mdaffarh005-arch/smart-billiard-lighting/3D Design/BOTTOM View.png

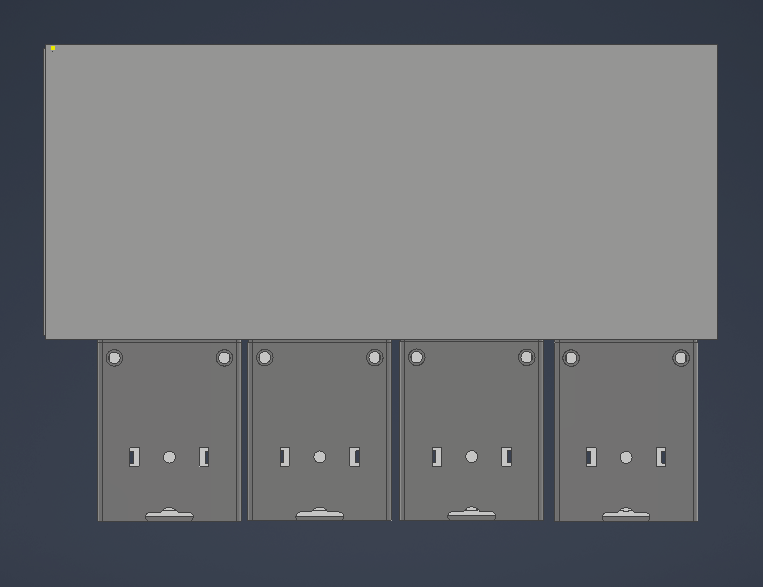
3D Design/BOTTOM View.png
