mdaffarh005-arch/smart-billiard-lighting/3D Design/FRONT View.png

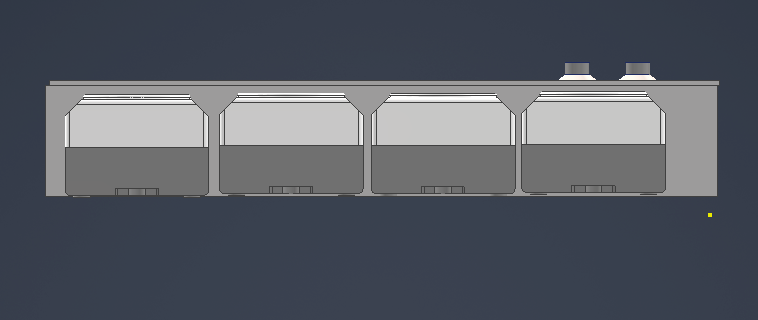
3D Design/FRONT View.png
