mdaffarh005-arch/smart-billiard-lighting/3D Design/LEFT View.png

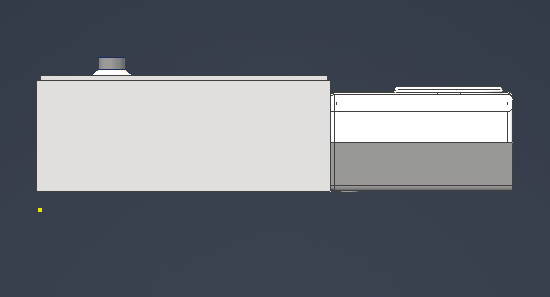
3D Design/LEFT View.png
