mdaffarh005-arch/smart-billiard-lighting/3D Design/RIGHT View.png

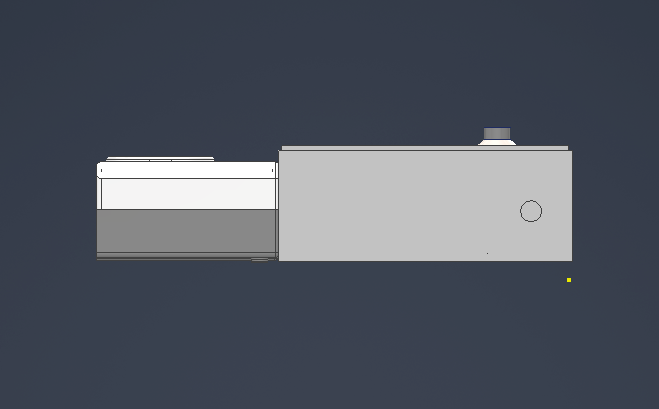
3D Design/RIGHT View.png
