mdaffarh005-arch/smart-billiard-lighting/3D Design/TOP Without Box Cover View.png

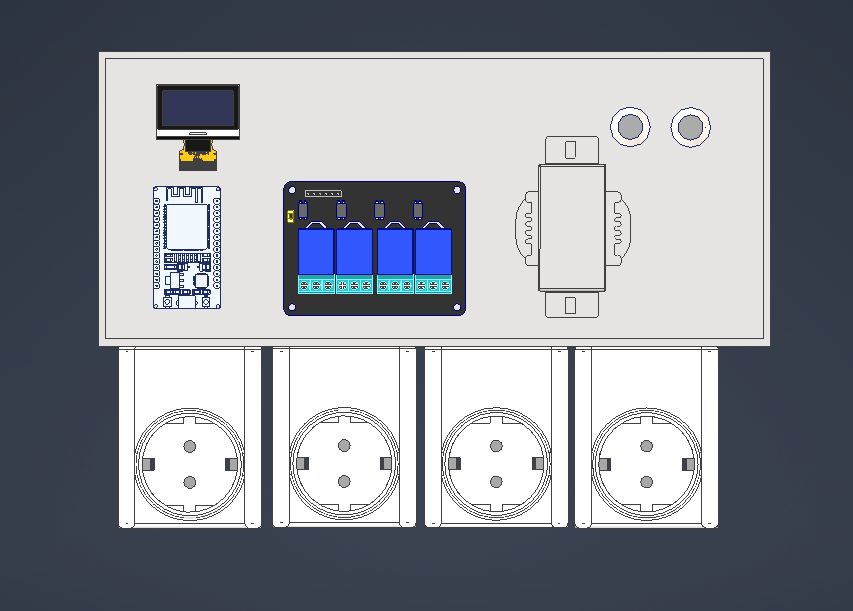
3D Design/TOP Without Box Cover View.png
