mdaffarh005-arch/smart-billiard-lighting/Blok Diagram/Diagram Blok.png

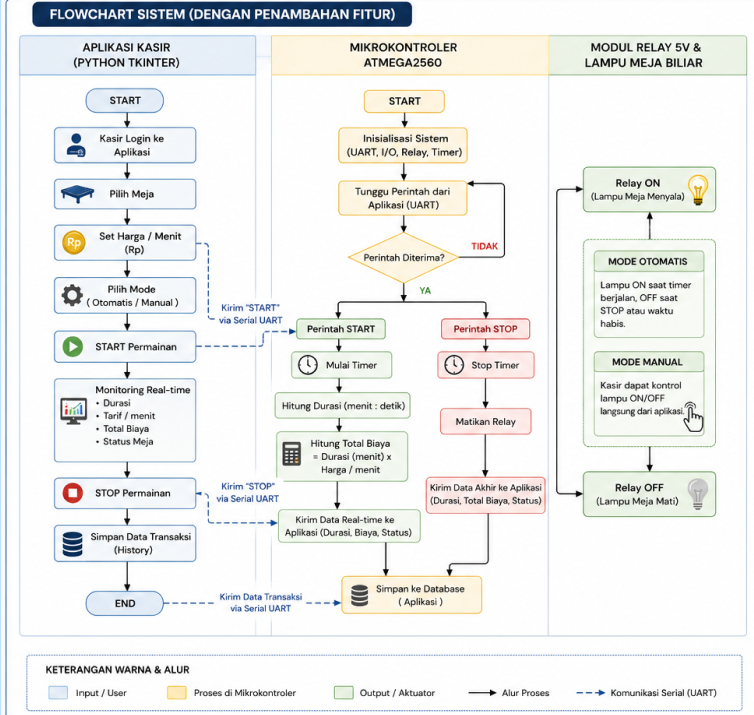
Blok Diagram/Diagram Blok.png
