mdaffarh005-arch/smart-billiard-lighting/Design UI UX/Mockup/desktop-billing V2.png

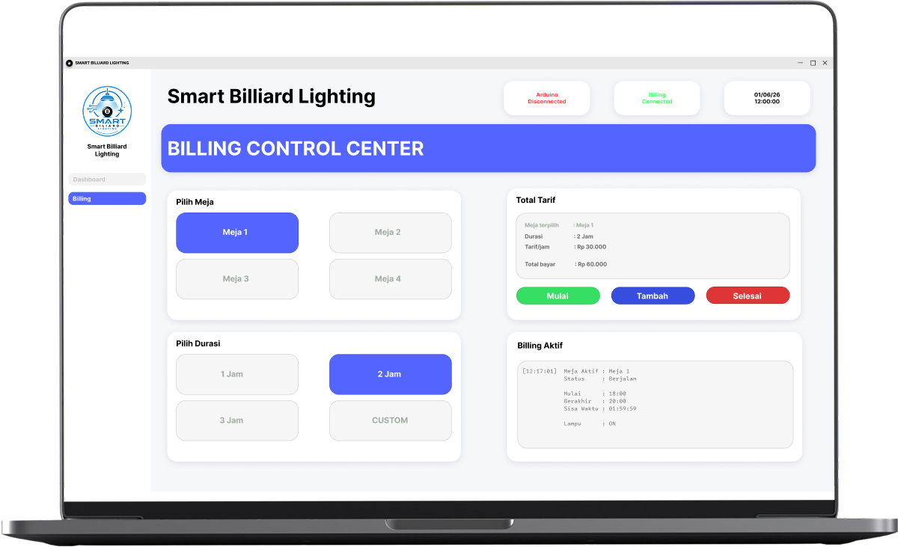
Design UI UX/Mockup/desktop-billing V2.png
