mdaffarh005-arch/smart-billiard-lighting/Design UI UX/Mockup/desktop-dashboard V2.png

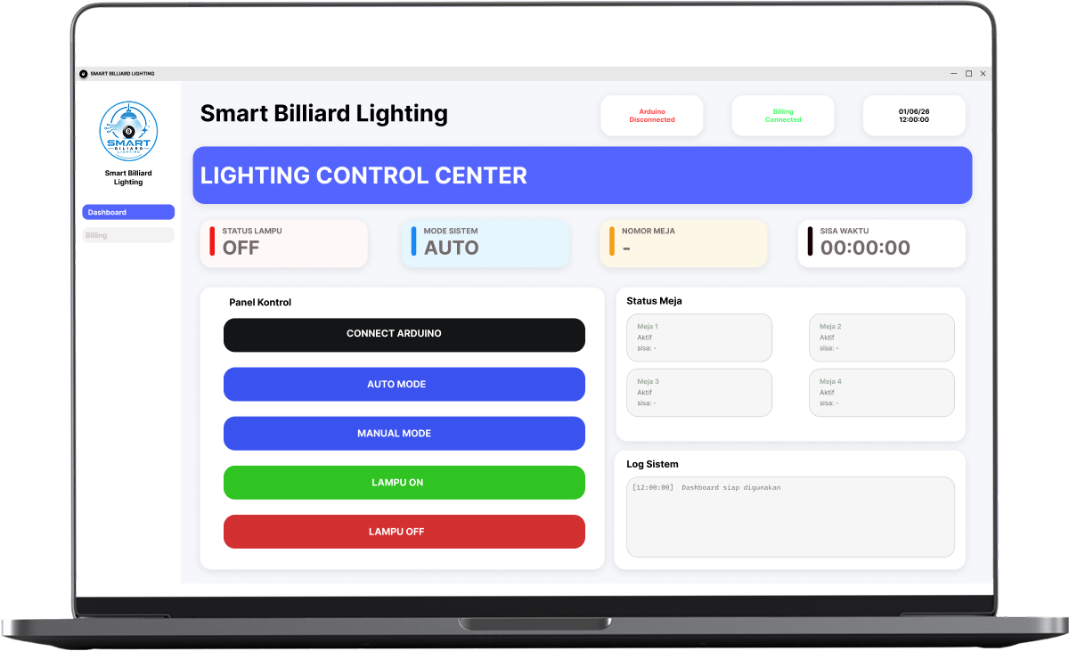
Design UI UX/Mockup/desktop-dashboard V2.png
