mdaffarh005-arch/smart-billiard-lighting/Design UI UX/Screenshot/BILLING.png

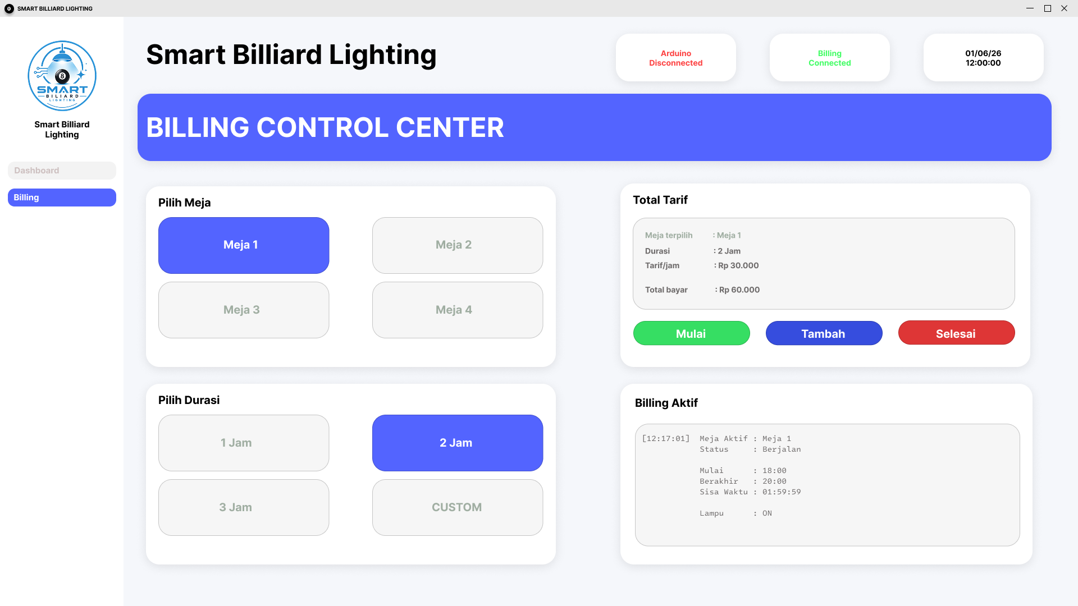
Design UI UX/Screenshot/BILLING.png
