mdaffarh005-arch/smart-billiard-lighting/Design UI UX/Screenshot/screenshot-billing.png

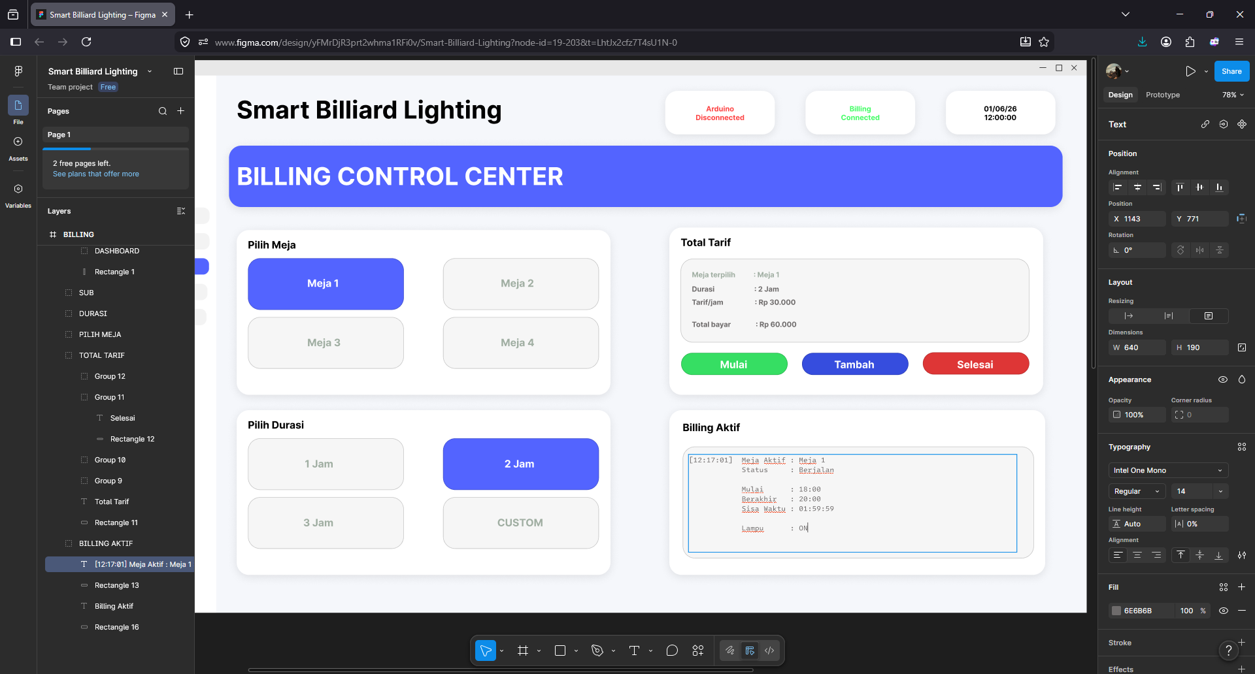
Design UI UX/Screenshot/screenshot-billing.png
