mdaffarh005-arch/smart-billiard-lighting/Design UI UX/Screenshot/screenshot-workspace.png

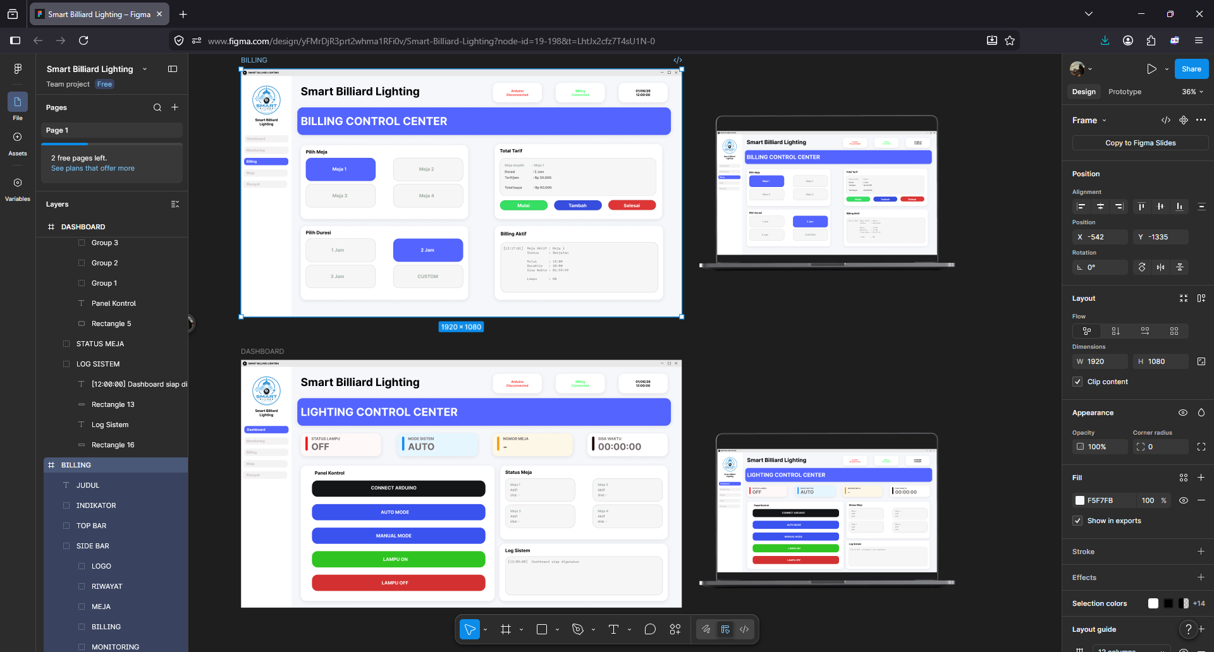
Design UI UX/Screenshot/screenshot-workspace.png
