mdaffarh005-arch/smart-billiard-lighting/Hardware/3D view bottom-smart-biliard-lighting.png

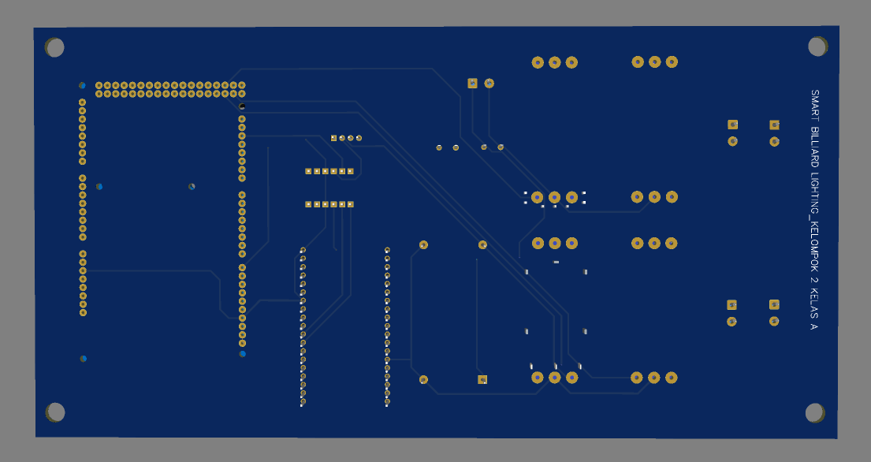
Hardware/3D view bottom-smart-biliard-lighting.png
