mdaffarh005-arch/smart-billiard-lighting/Hardware/3D view top-smart-biliard-lighting.png

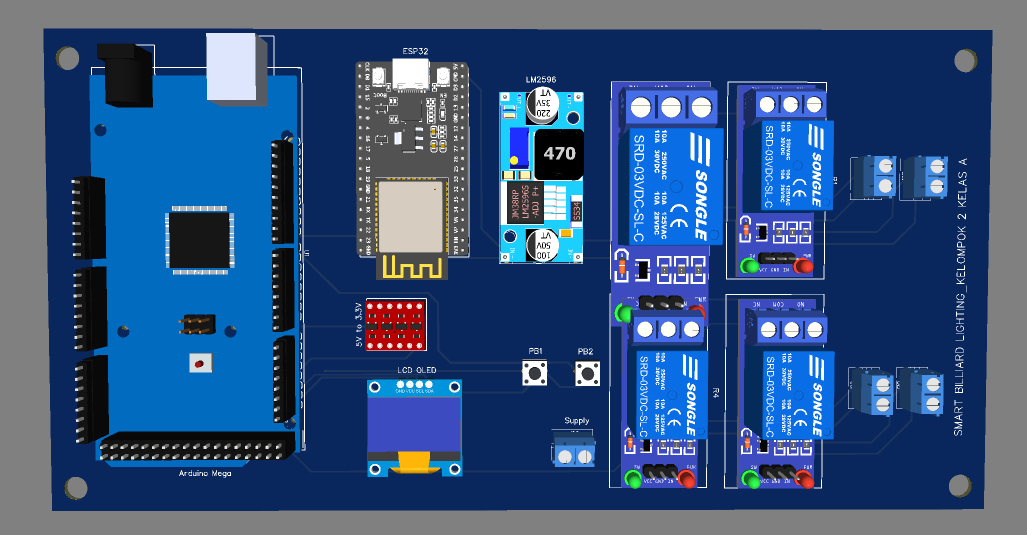
Hardware/3D view top-smart-biliard-lighting.png
