mdaffarh005-arch/smart-billiard-lighting/Hardware/Desain-PCB-smart-biliard-lighting.png

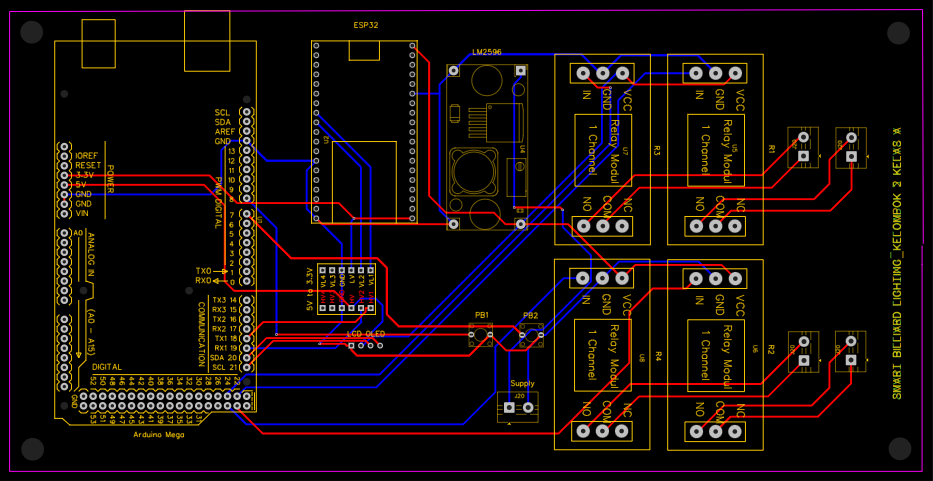
Hardware/Desain-PCB-smart-biliard-lighting.png
