mdaffarh005-arch/smart-billiard-lighting/Mindmap/Mindmap Project Kelompok SBL.jpeg

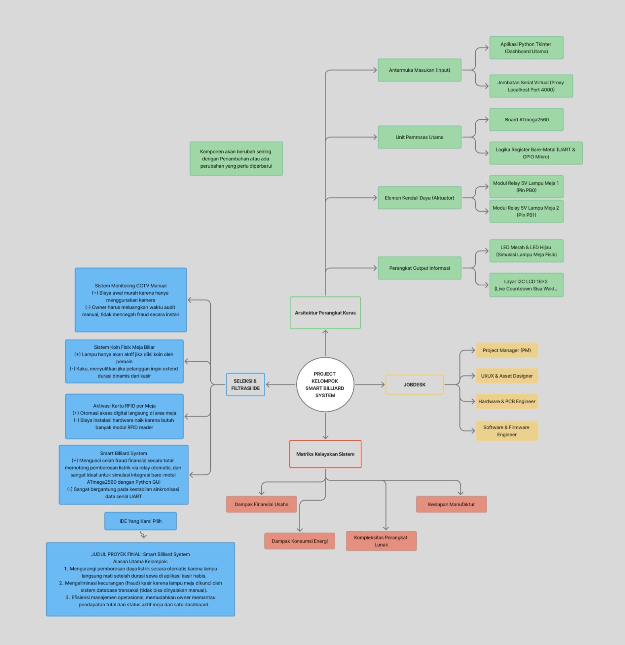
Mindmap/Mindmap Project Kelompok SBL.jpeg
